Active-Learning-Kyle/solar-weather-station/docs/images/readme/prototype-complete.webp

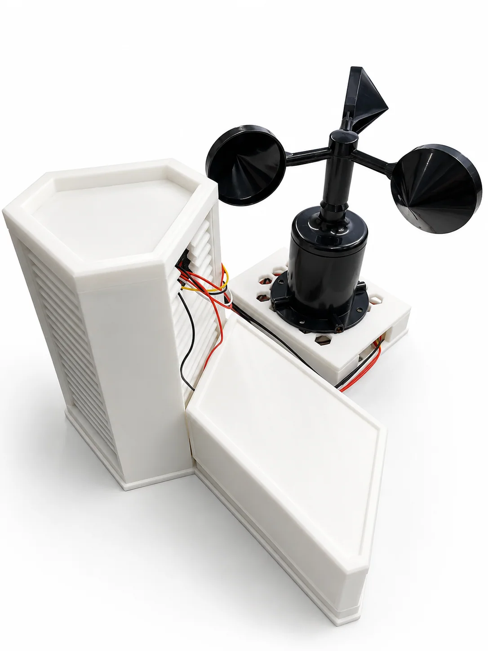
docs/images/readme/prototype-complete.webp
