Active-Learning-Kyle/solar-weather-station/hardware/cad/images/main-body-shell-cad.png

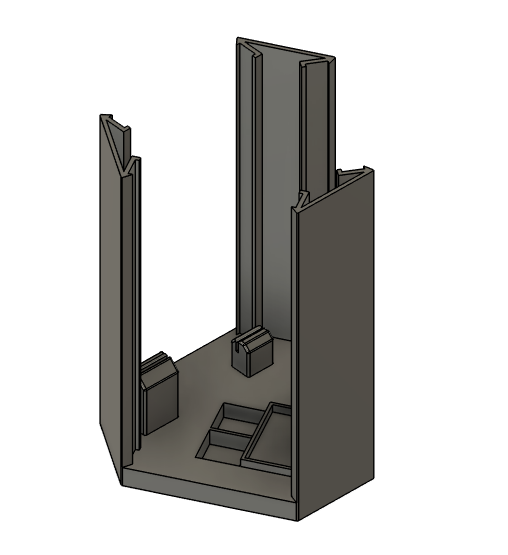
hardware/cad/images/main-body-shell-cad.png
