Active-Learning-Kyle/solar-weather-station/hardware/cad/images/power-module-closed.jpg

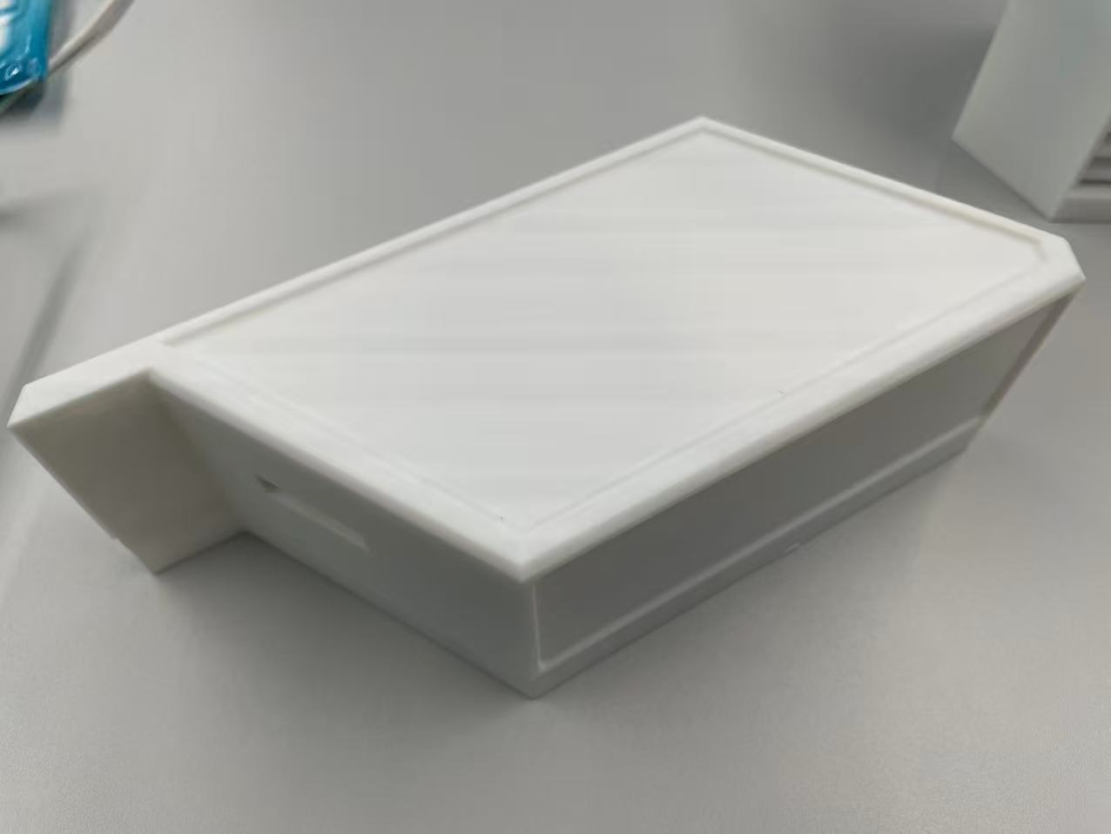
hardware/cad/images/power-module-closed.jpg
