Active-Learning-Kyle/solar-weather-station/hardware/cad/images/power-module-mount-cad.png

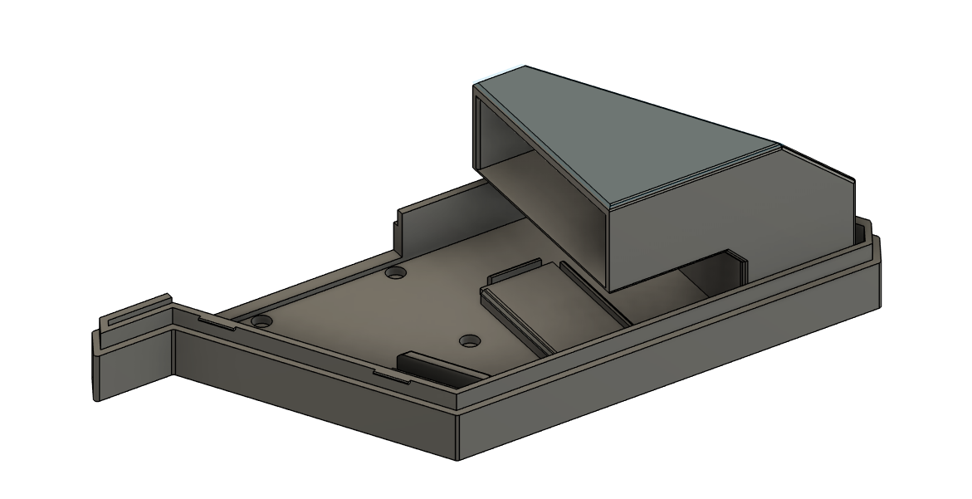
hardware/cad/images/power-module-mount-cad.png
