Active-Learning-Kyle/solar-weather-station/hardware/cad/images/sensor-rod-lid-cad.png

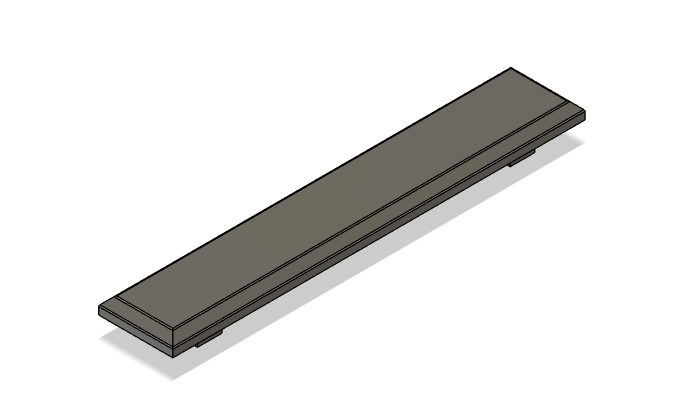
hardware/cad/images/sensor-rod-lid-cad.png
