Active-Learning-Kyle/solar-weather-station/hardware/cad/images/station-body-assembled-front.jpg

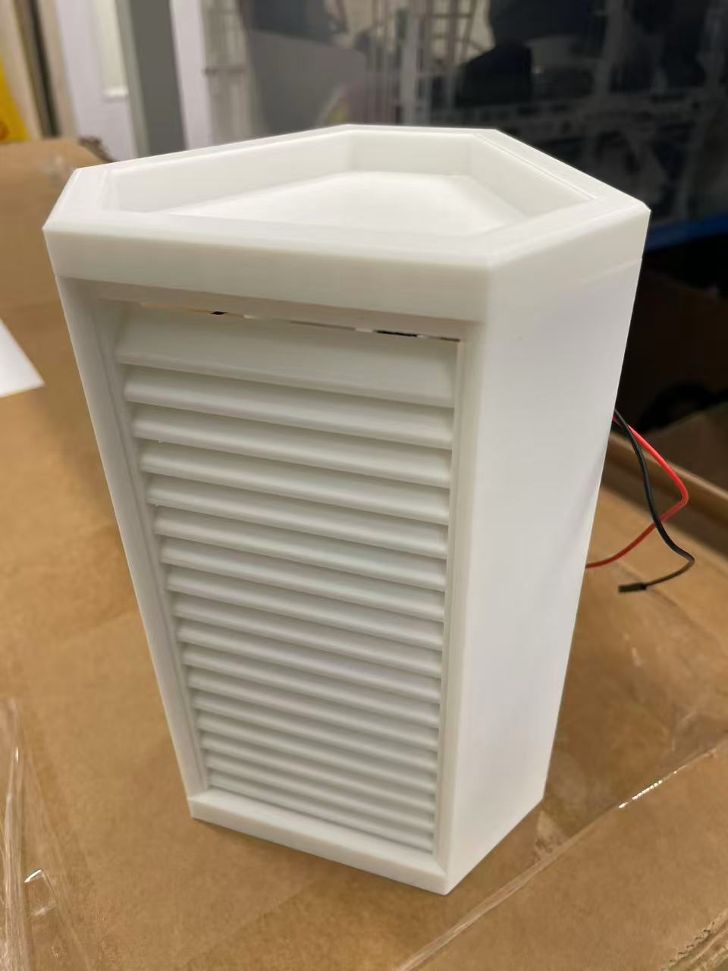
hardware/cad/images/station-body-assembled-front.jpg
